4th-High-School-of-Trikala/3d-printed-accessibility-map/3DMapTrikala/photos/map-7.jpeg

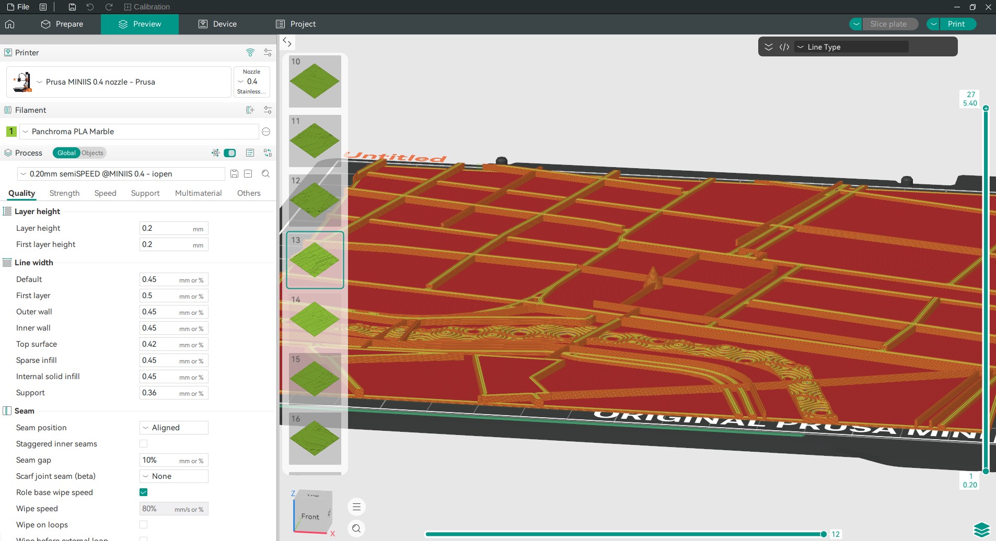
3DMapTrikala/photos/map-7.jpeg
