4th-High-School-of-Trikala/3d-printed-accessibility-map/3DMapTrikala/photos/map-22.png

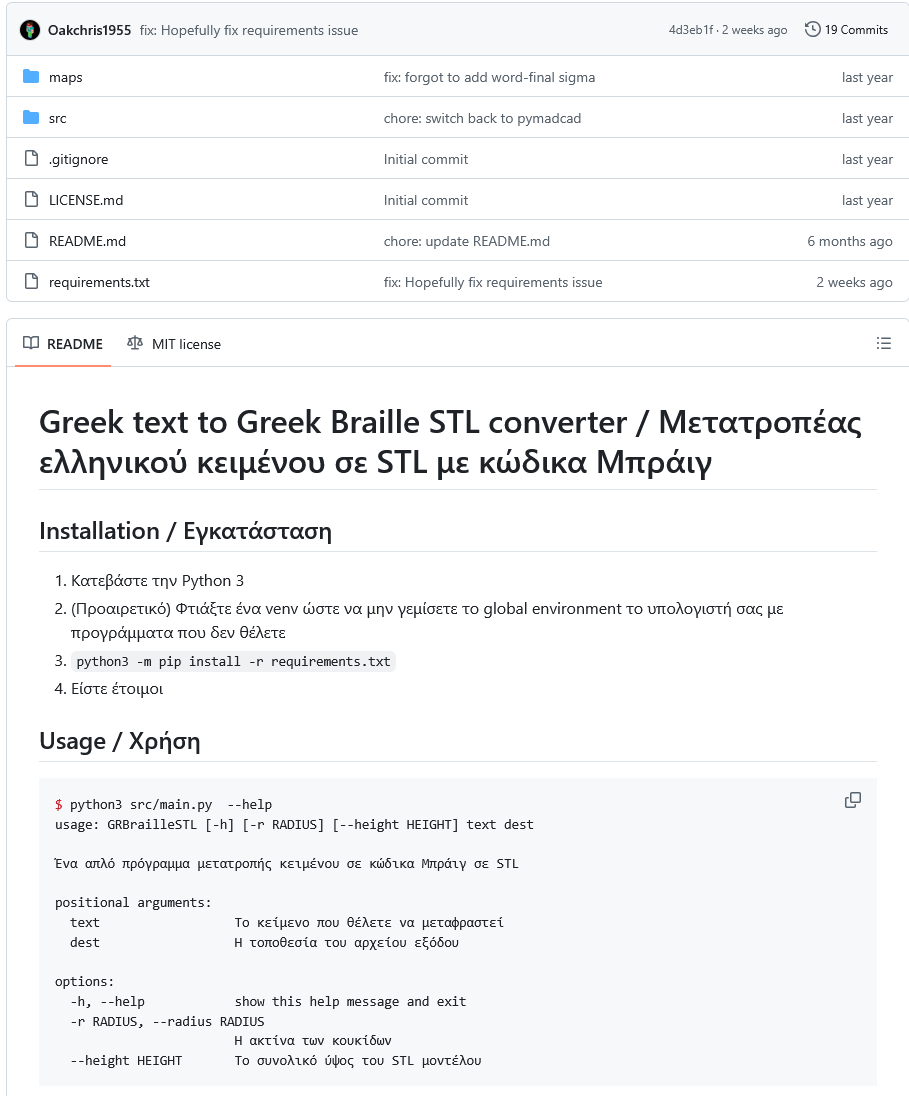
3DMapTrikala/photos/map-22.png
