4th-High-School-of-Trikala/3d-printed-accessibility-map/3DMapTrikala/photos/map-25.jpg

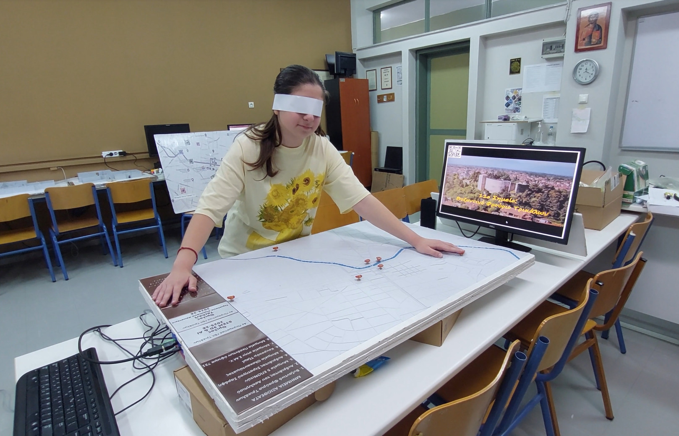
3DMapTrikala/photos/map-25.jpg
