4th-High-School-of-Trikala/3d-printed-accessibility-map/3dSchoolFloorPlan/photos/floor-plan-18-2.jpg

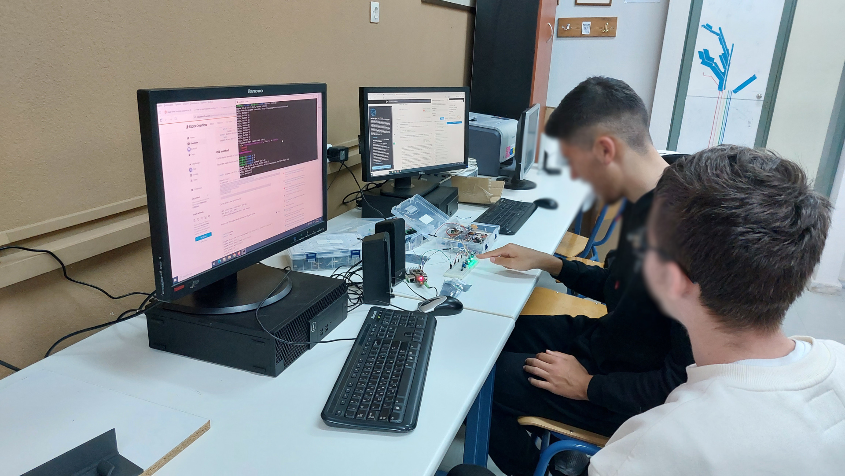
3dSchoolFloorPlan/photos/floor-plan-18-2.jpg
