4th-High-School-of-Trikala/3d-printed-accessibility-map/3dSchoolFloorPlan/photos/floorplan-inkscape-3.jpg

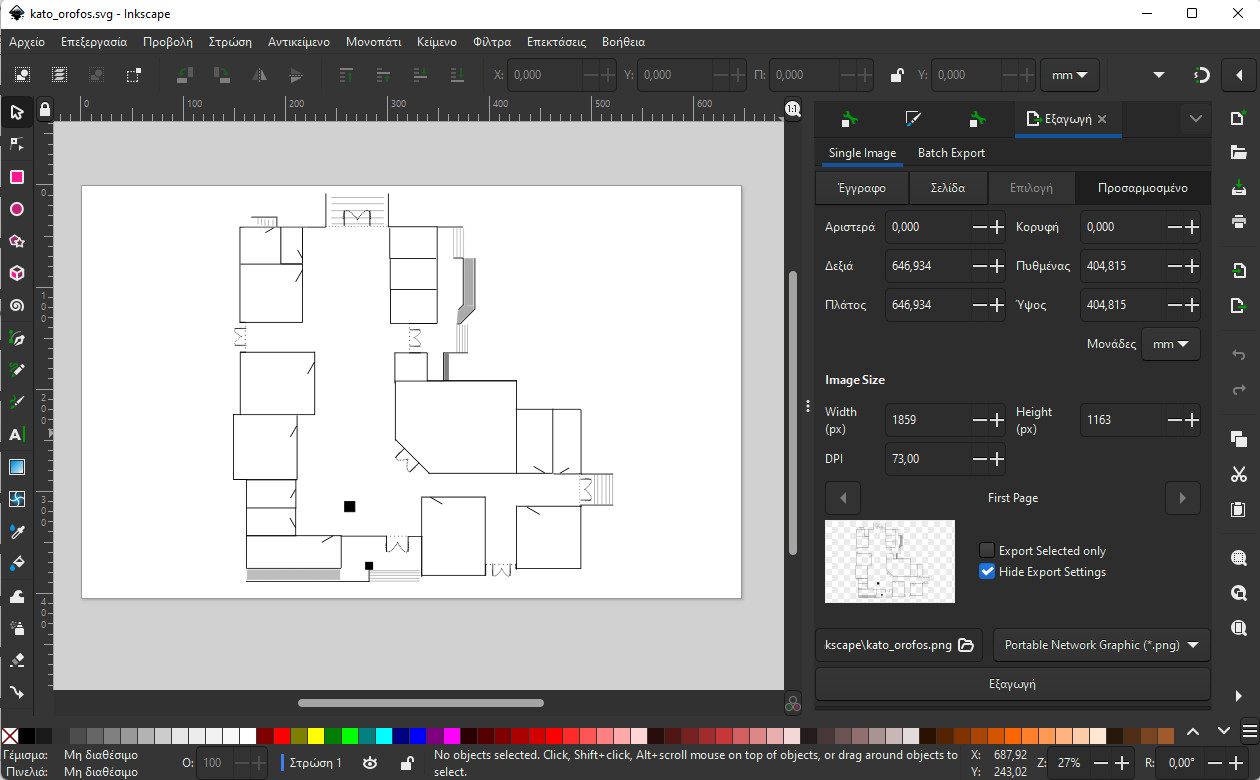
3dSchoolFloorPlan/photos/floorplan-inkscape-3.jpg
