4th-High-School-of-Trikala/3d-printed-accessibility-map/3dSchoolFloorPlan/photos/ylika-plan1.jpg

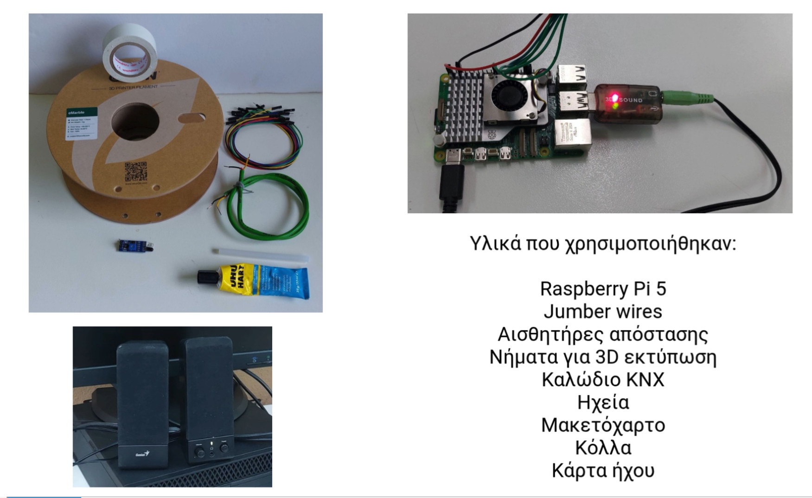
3dSchoolFloorPlan/photos/ylika-plan1.jpg
