4th-High-School-of-Trikala/3d-printed-accessibility-map/3DMapTrikala/assets/stl/Trikala-p100X-m200Y.stl

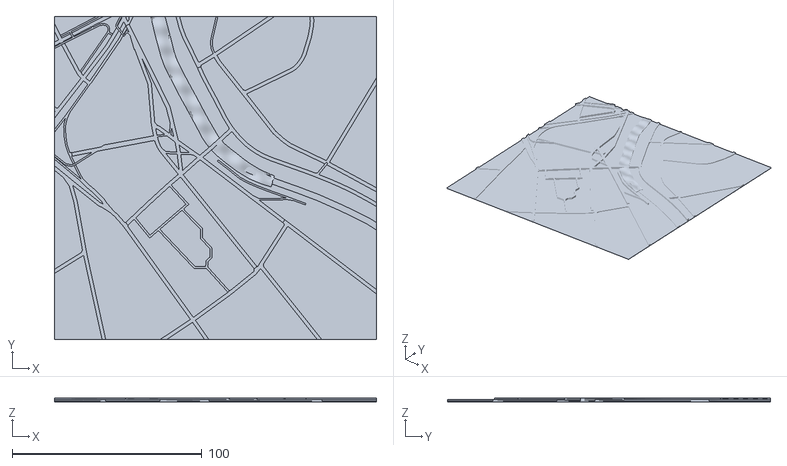
[picture p78: CAD file, 2026-05-27]
3DMapTrikala/assets/stl/Trikala-p100X-m200Y.stl
169.8 x 170.5 x 2.12
